SuperHouse/FSI6CAN/Images/2019-01-12_22-10-29.jpg

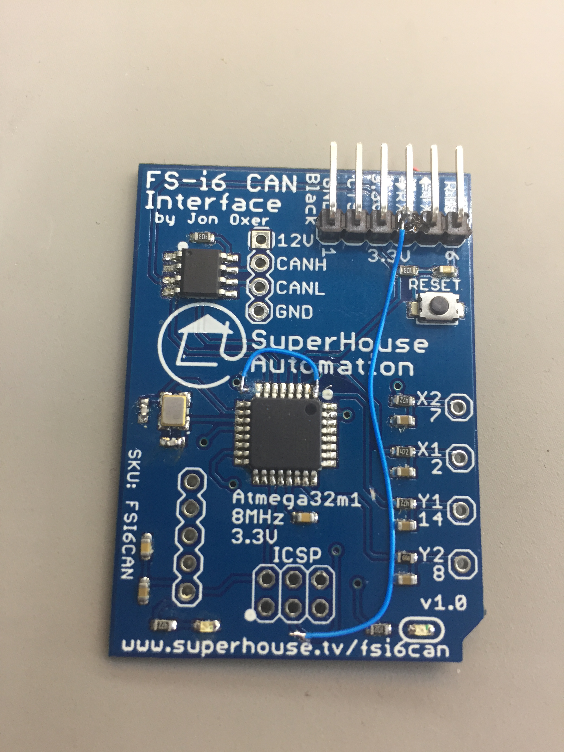
Images/2019-01-12_22-10-29.jpg
