SuperHouse/FSI6CAN/Images/2019-01-18_22-01-29.jpg

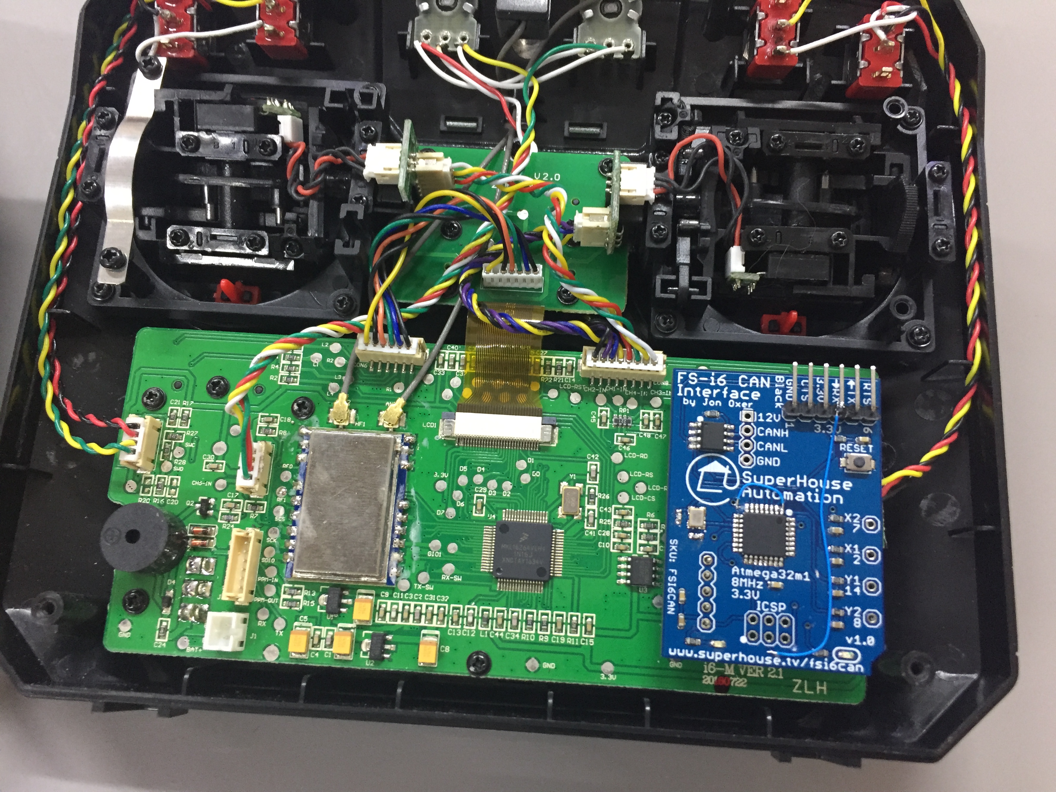
Images/2019-01-18_22-01-29.jpg
