SuperHouse/FSI6CAN/Images/2019-01-18_22-02-20.jpg

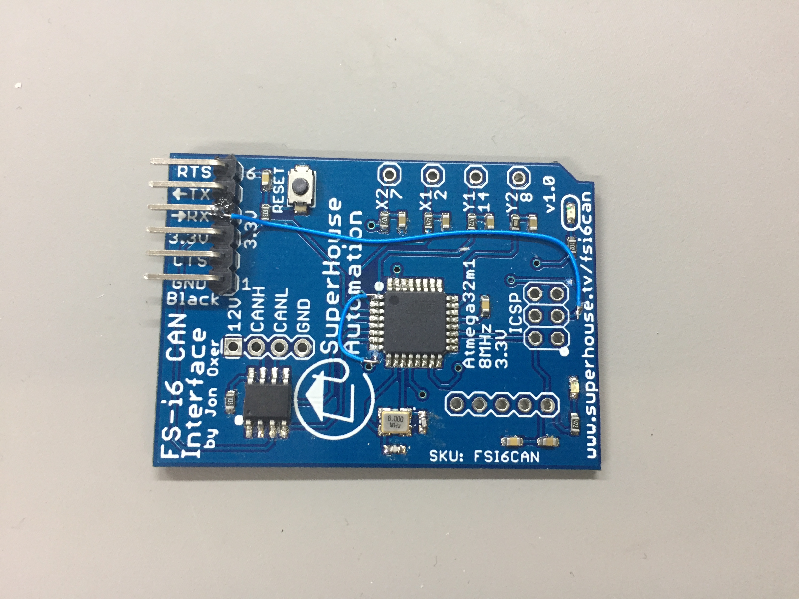
Images/2019-01-18_22-02-20.jpg
